Marsbitware/yumiko/camera_app/assets/styles/cyberpunk.png

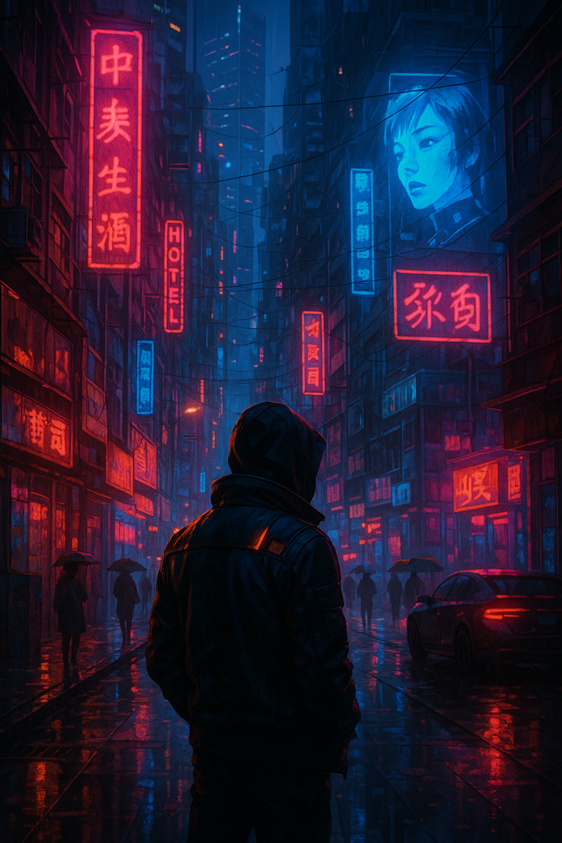
camera_app/assets/styles/cyberpunk.png
