Marsbitware/yumiko/camera_app/assets/styles/horror.png

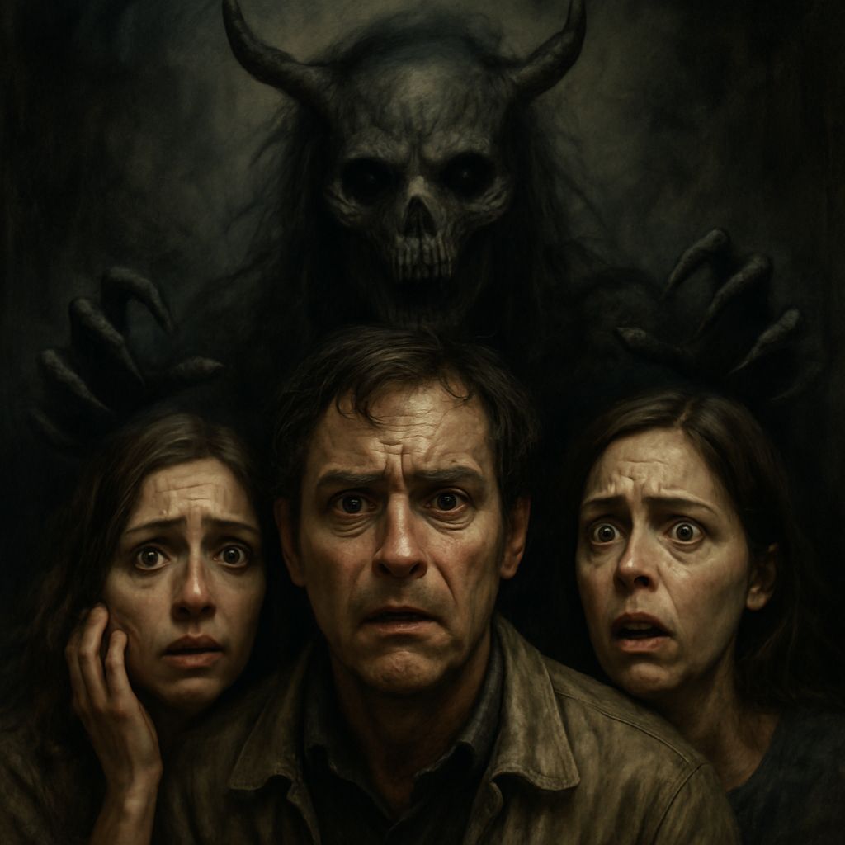
camera_app/assets/styles/horror.png
