Marsbitware/yumiko/camera_app/assets/styles/mafiosi.png

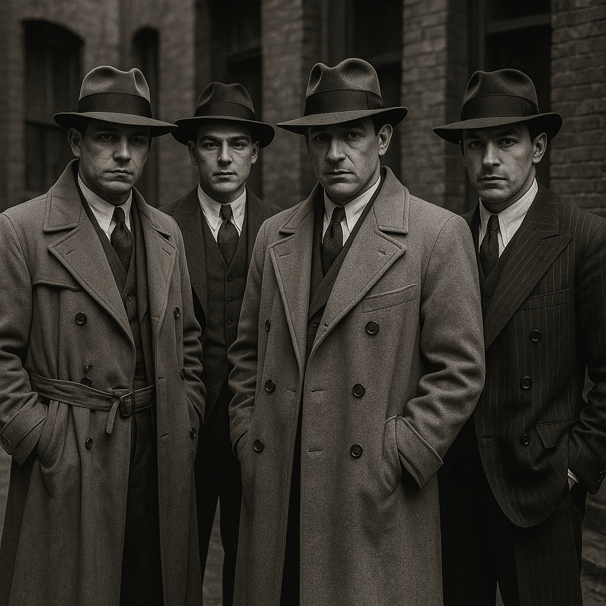
camera_app/assets/styles/mafiosi.png
