Marsbitware/yumiko/camera_app/assets/styles/medieval.jpg

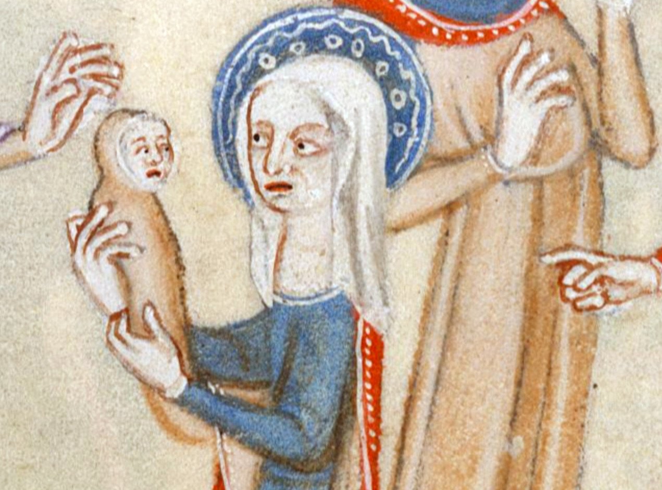
camera_app/assets/styles/medieval.jpg
