Marsbitware/yumiko/camera_app/assets/styles/minecraft.png

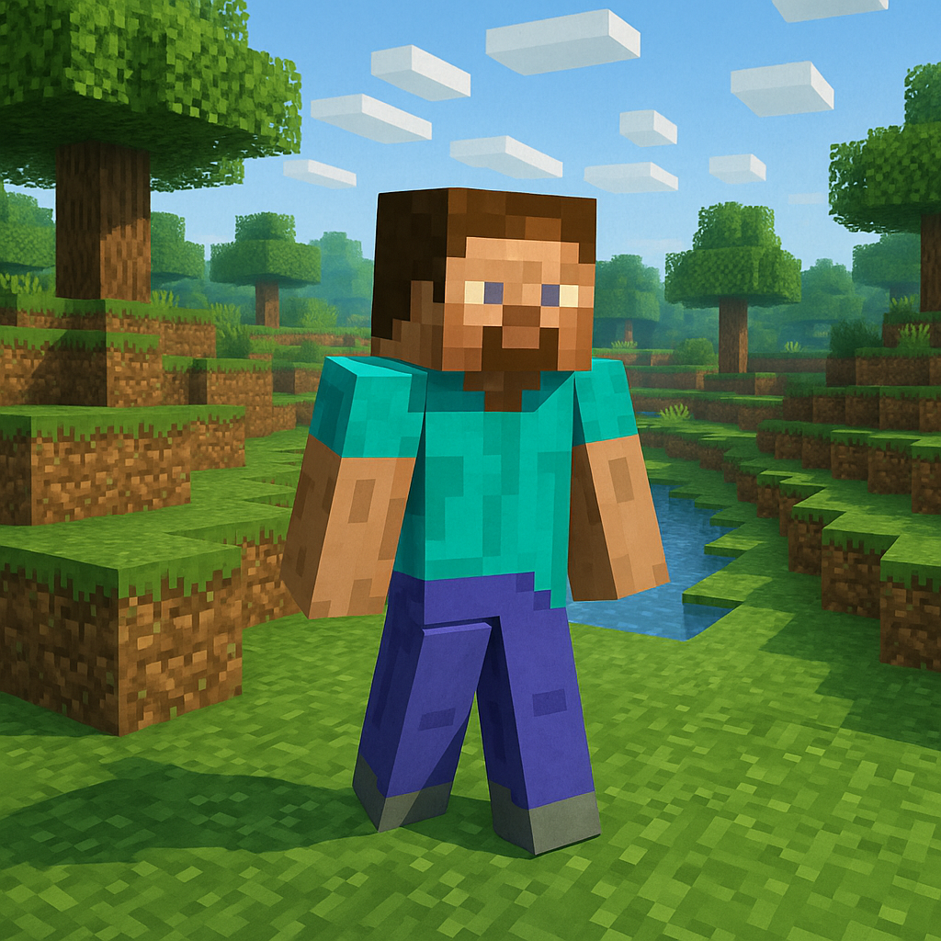
camera_app/assets/styles/minecraft.png
