Marsbitware/yumiko/camera_app/assets/styles/random.png

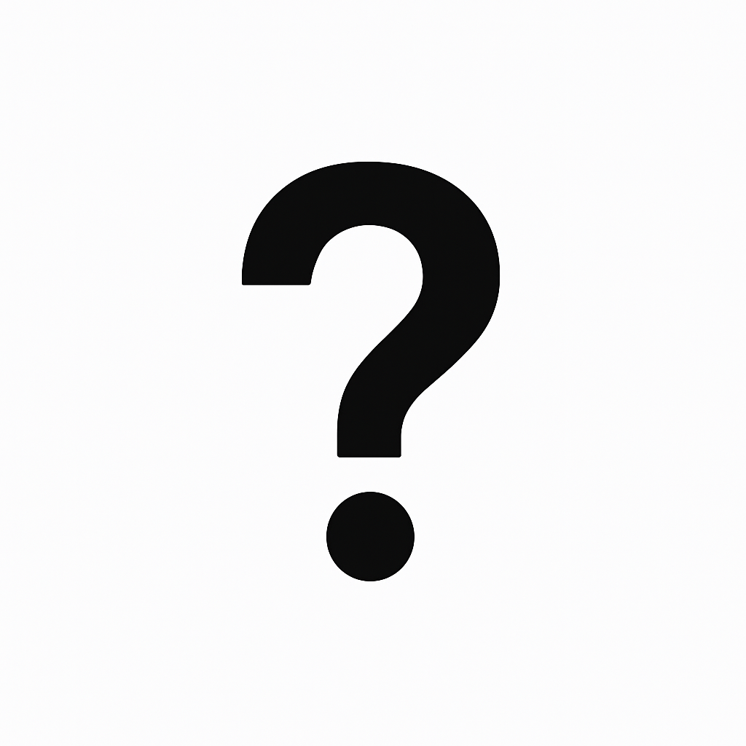
camera_app/assets/styles/random.png
