Marsbitware/yumiko/camera_app/assets/styles/roman_empire.png

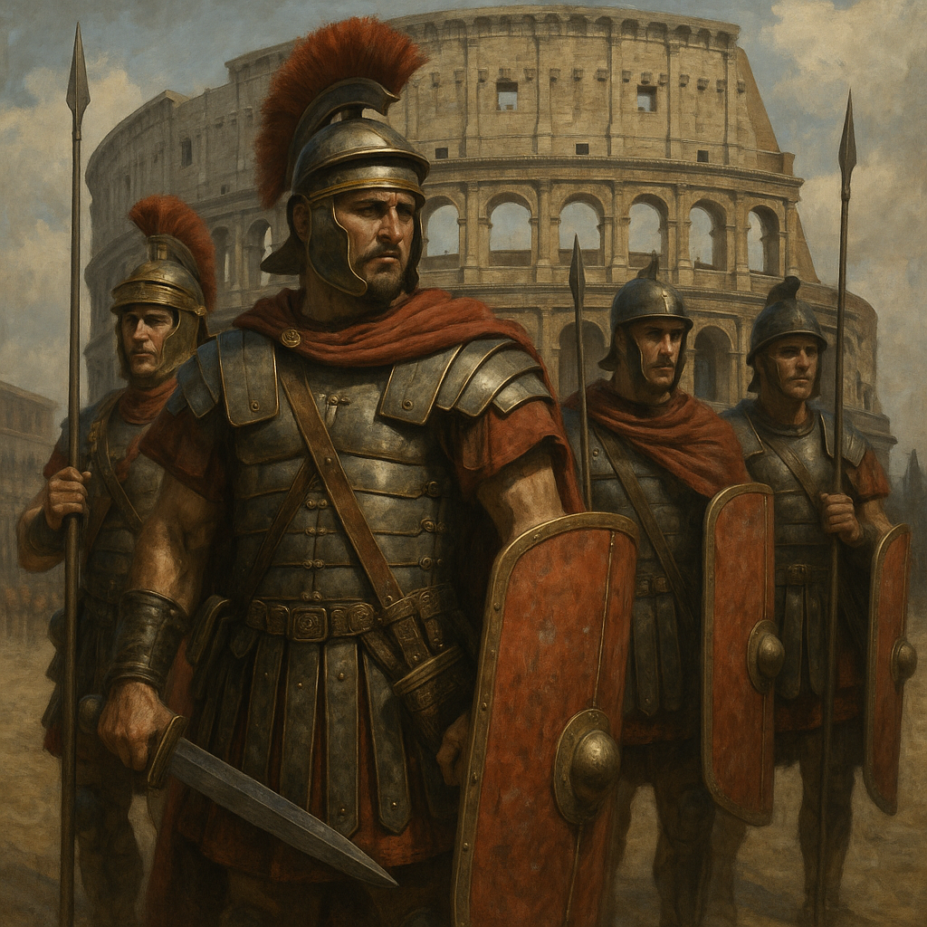
camera_app/assets/styles/roman_empire.png
