Marsbitware/yumiko/camera_app/assets/styles/simpsons.jpg

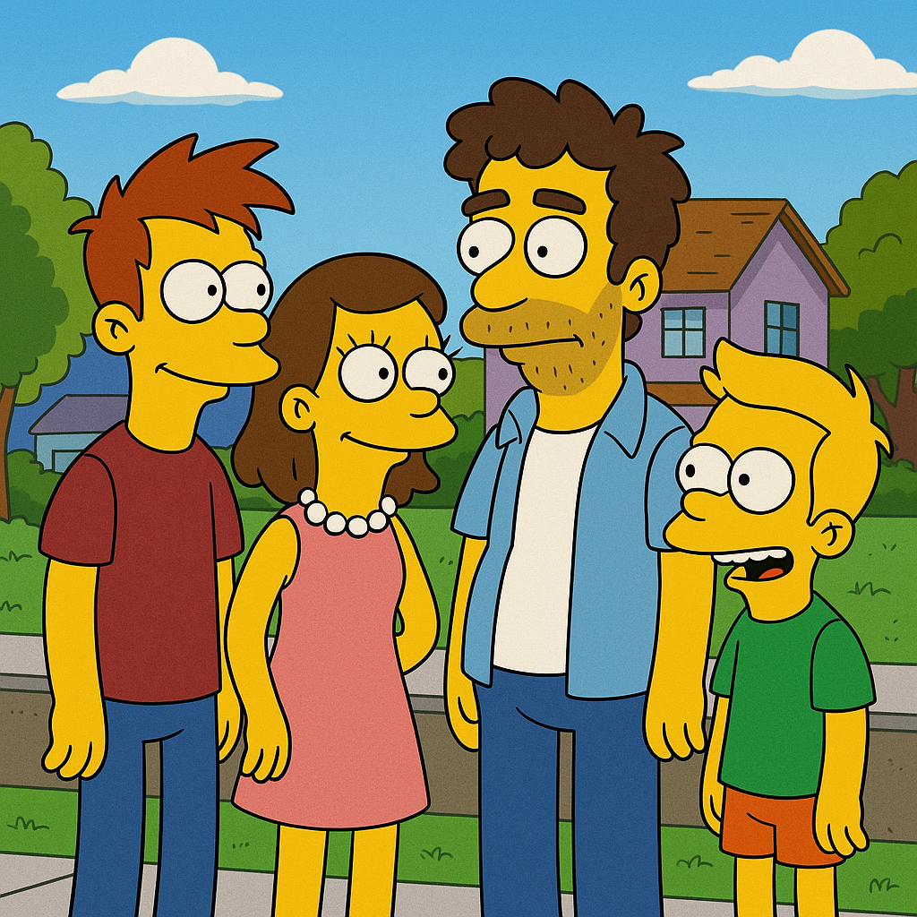
camera_app/assets/styles/simpsons.jpg
