Marsbitware/yumiko/camera_app/assets/styles/star_wars.png

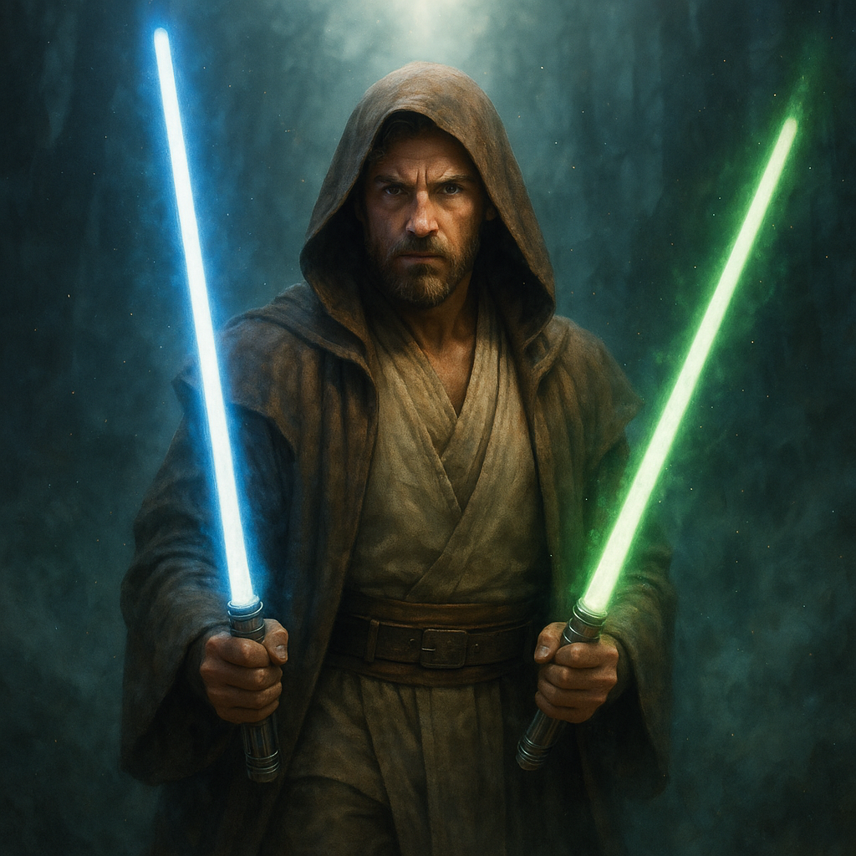
camera_app/assets/styles/star_wars.png
