Marsbitware/yumiko/camera_app/assets/styles/steampunk.png

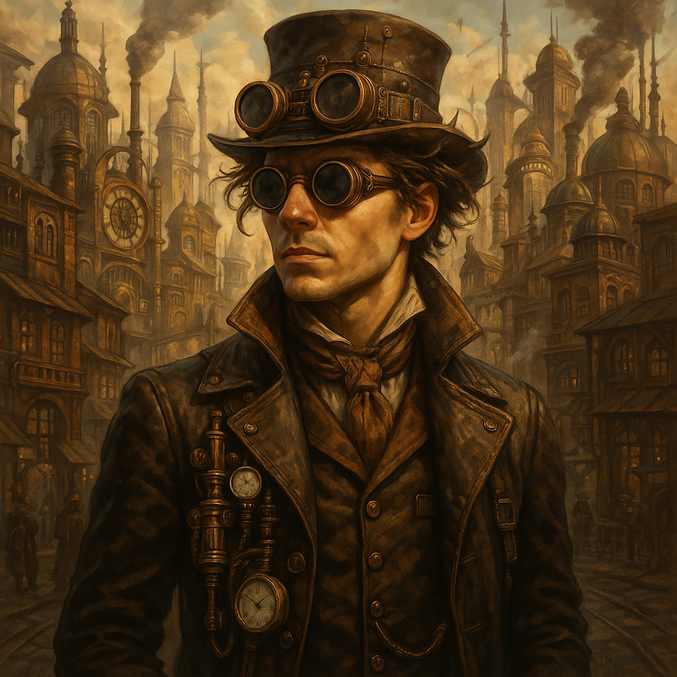
camera_app/assets/styles/steampunk.png
