Marsbitware/yumiko/camera_app/assets/styles/studio_ghibli.jpg

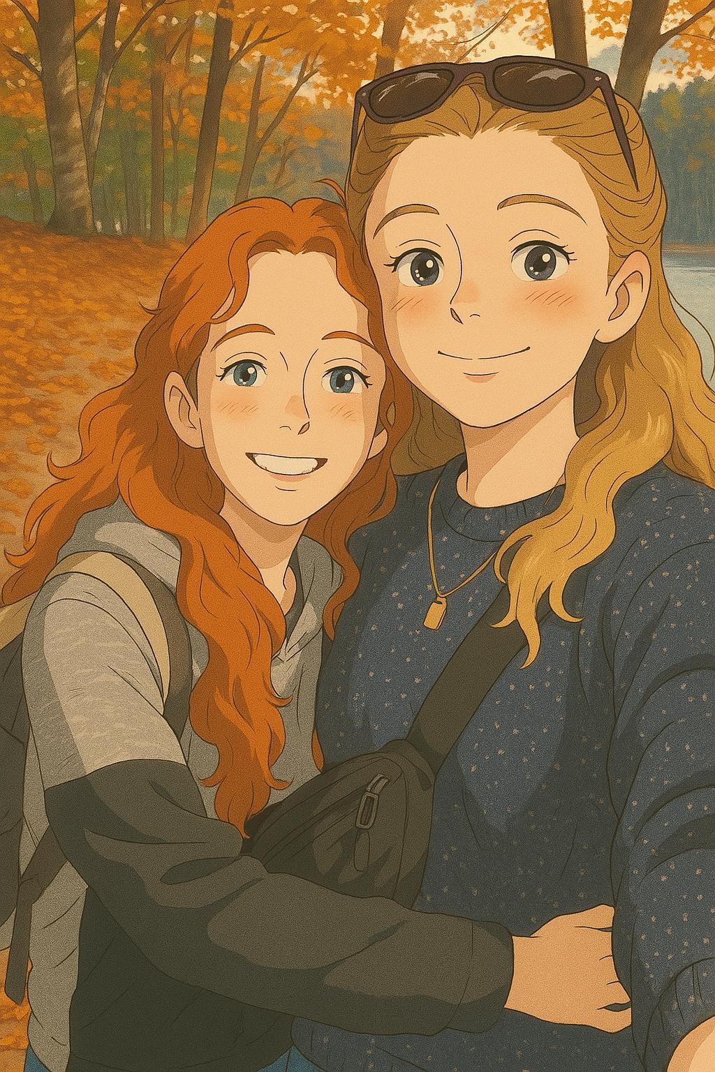
camera_app/assets/styles/studio_ghibli.jpg
